delikeeb/support/_extras/vanana/rev2.5_GB/ARC case/sheetImages.JPG

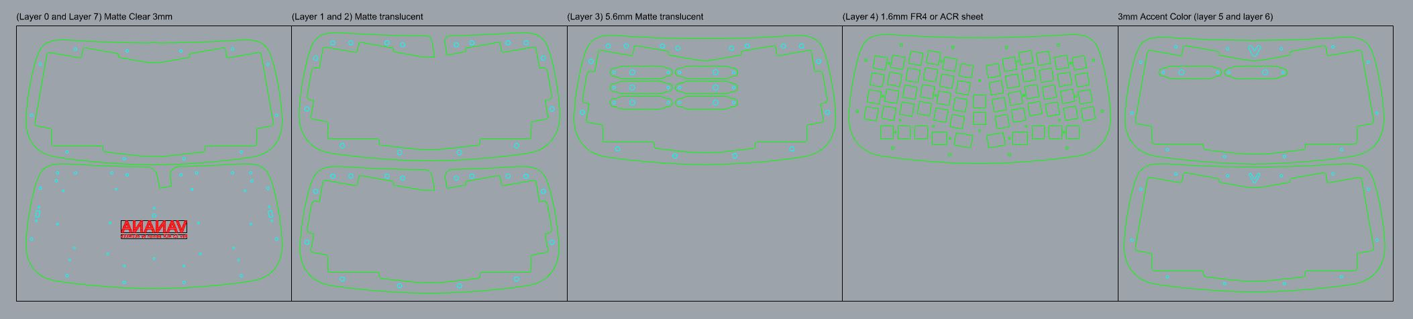
_extras/vanana/rev2.5_GB/ARC case/sheetImages.JPG
