delikeeb/support/buildGuide/Vanana/Vanana-BuildGuide-rev2.5.assets/13-PlateScrew@2x.png

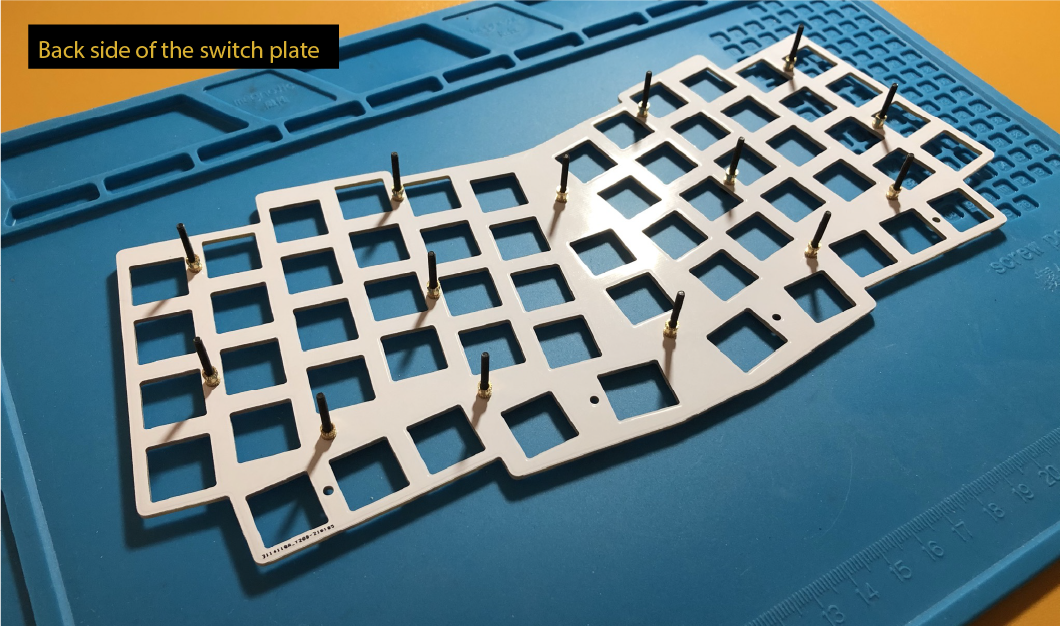
buildGuide/Vanana/Vanana-BuildGuide-rev2.5.assets/13-PlateScrew@2x.png
